KenNotSad/Numpad-Projectv1/cad/R2-3_2u.SLDPRT

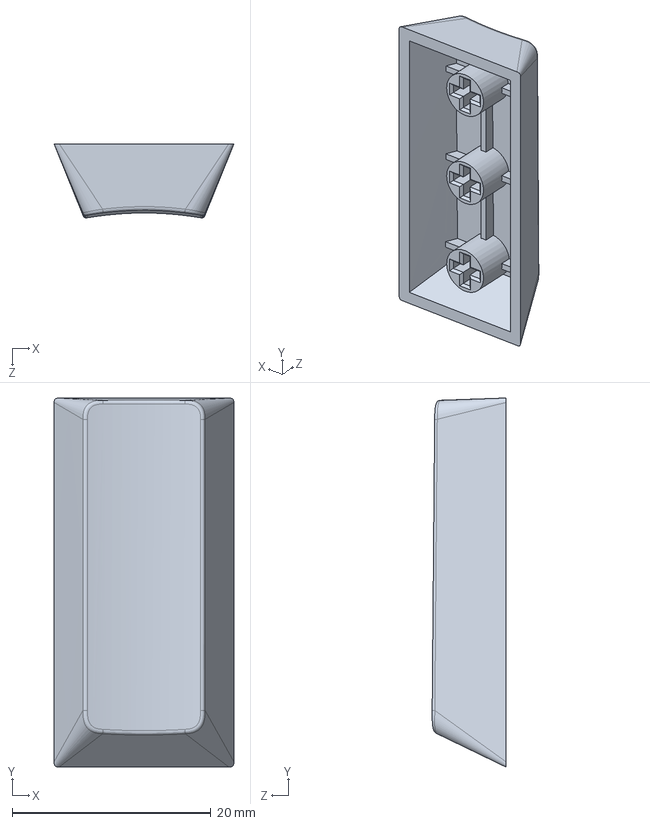
[picture p14: CAD file, 2026-06-09]
cad/R2-3_2u.SLDPRT
18.1 x 37.1 x 7.42 mm
