KenNotSad/Numpad-Projectv1/cad/Cherry MX Keycap.SLDPRT

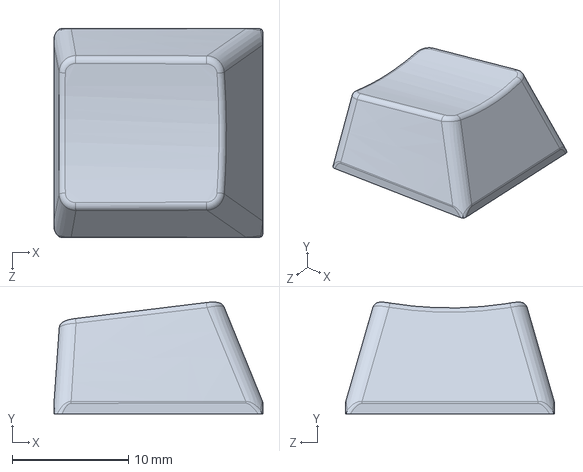
[picture p15: CAD file, 2026-06-09]
cad/Cherry MX Keycap.SLDPRT
18.0 x 9.64 x 18.0 mm
