KenNotSad/Numpad-Projectv1/cad/-R5_2u[1].SLDPRT

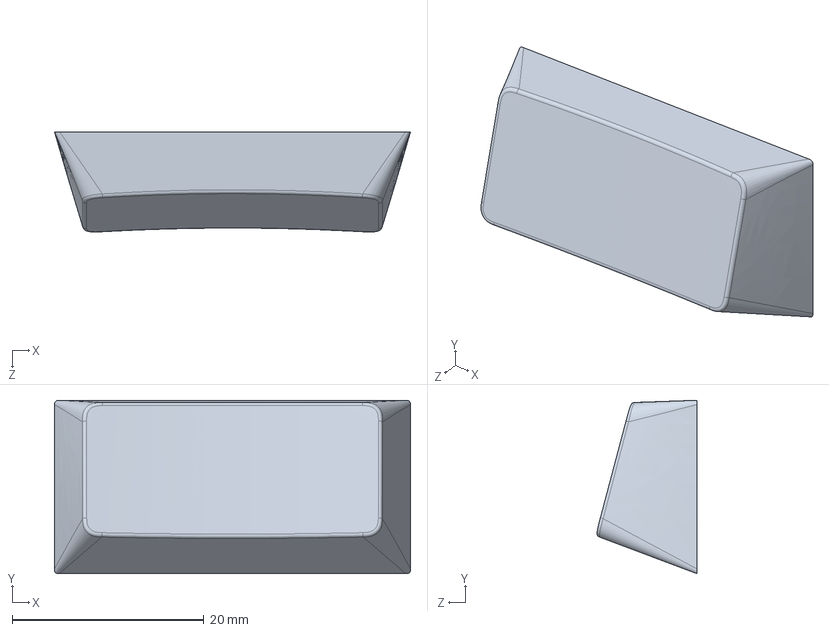
[picture p16: CAD file, 2026-06-09]
cad/-R5_2u[1].SLDPRT
37.2 x 18.1 x 10.4 mm
