KenNotSad/Numpad-Projectv1/cad/switch.step

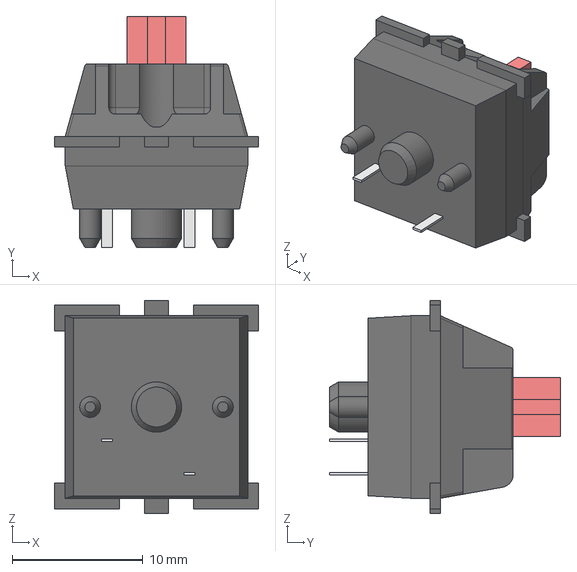
[picture p17: CAD file, 2026-05-14]
cad/switch.step
15.6 x 17.7 x 16.3 mm
